FlyFish0825/lamost_broad/just外接板/picture/QQ20260525-173408.png

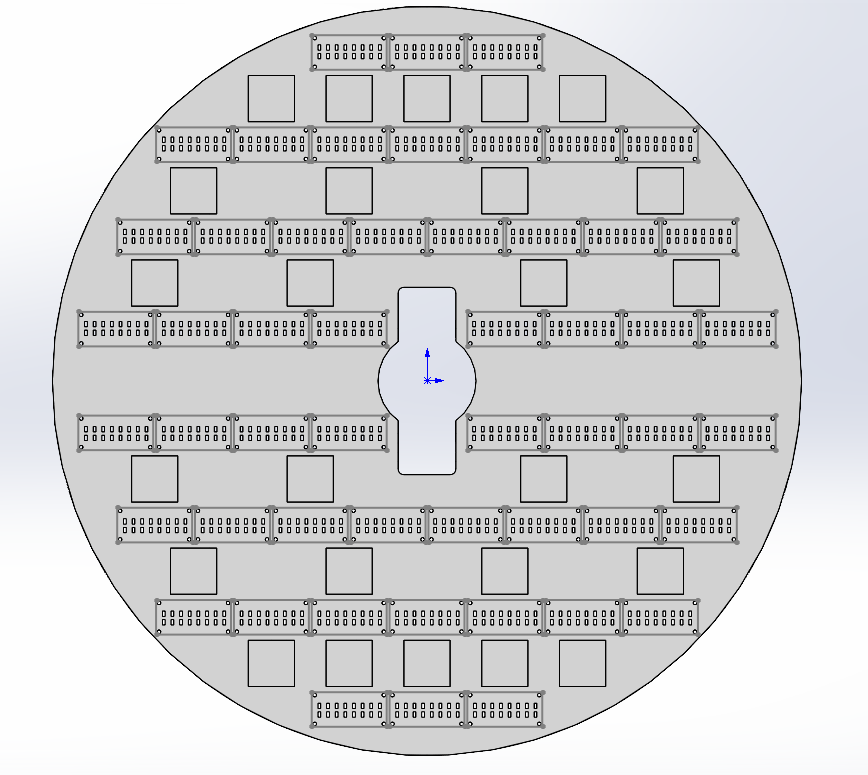
just外接板/picture/QQ20260525-173408.png
