FlyFish0825/lamost_broad/just外接板/picture/光纤示意2.png

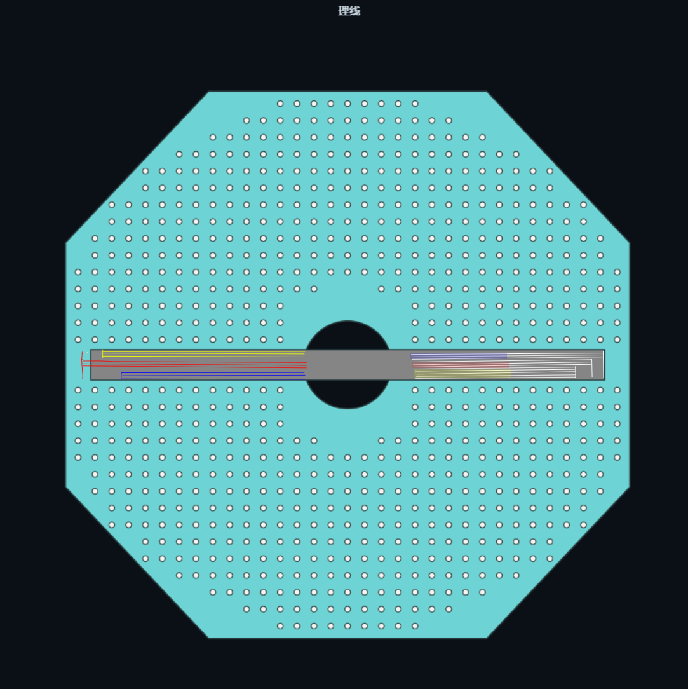
just外接板/picture/光纤示意2.png
