FlyFish0825/lamost_broad/just外接板/picture/光纤示意.png

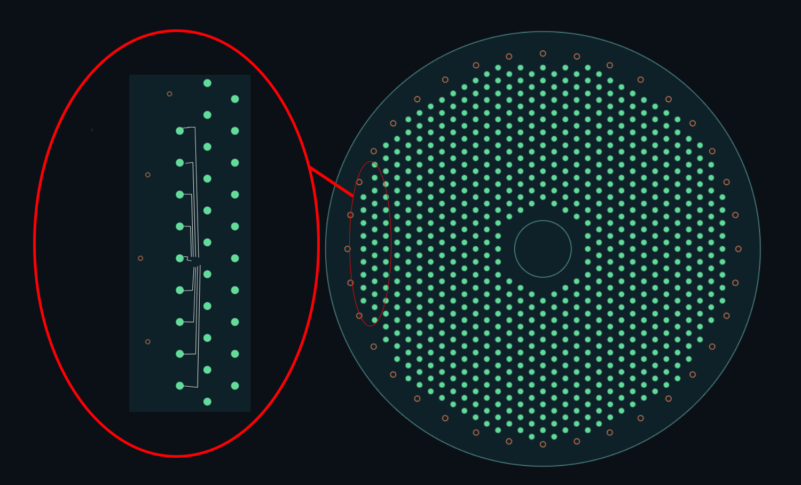
just外接板/picture/光纤示意.png
