FlyFish0825/lamost_broad/just外接板/picture/微信图片_20260402115239_76_106.jpg

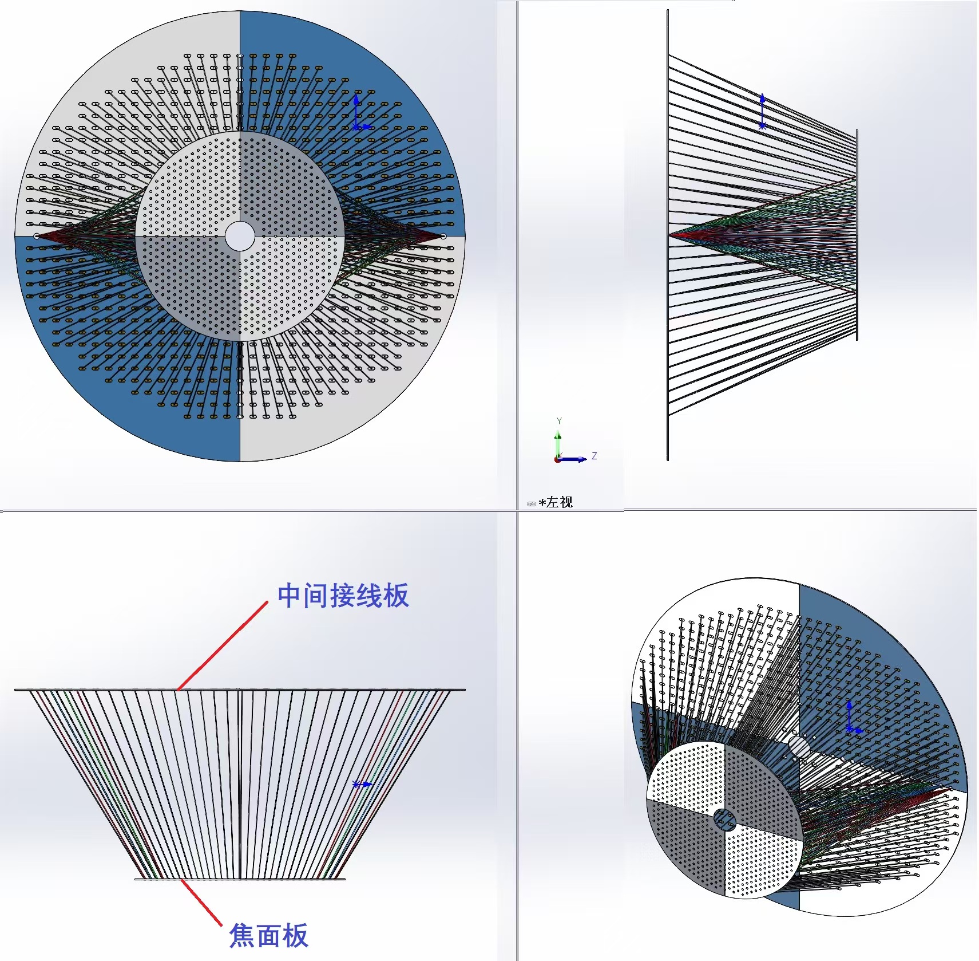
just外接板/picture/微信图片_20260402115239_76_106.jpg
