FlyFish0825/lamost_broad/just外接板/picture/微信图片_20260402115243_80_106.jpg

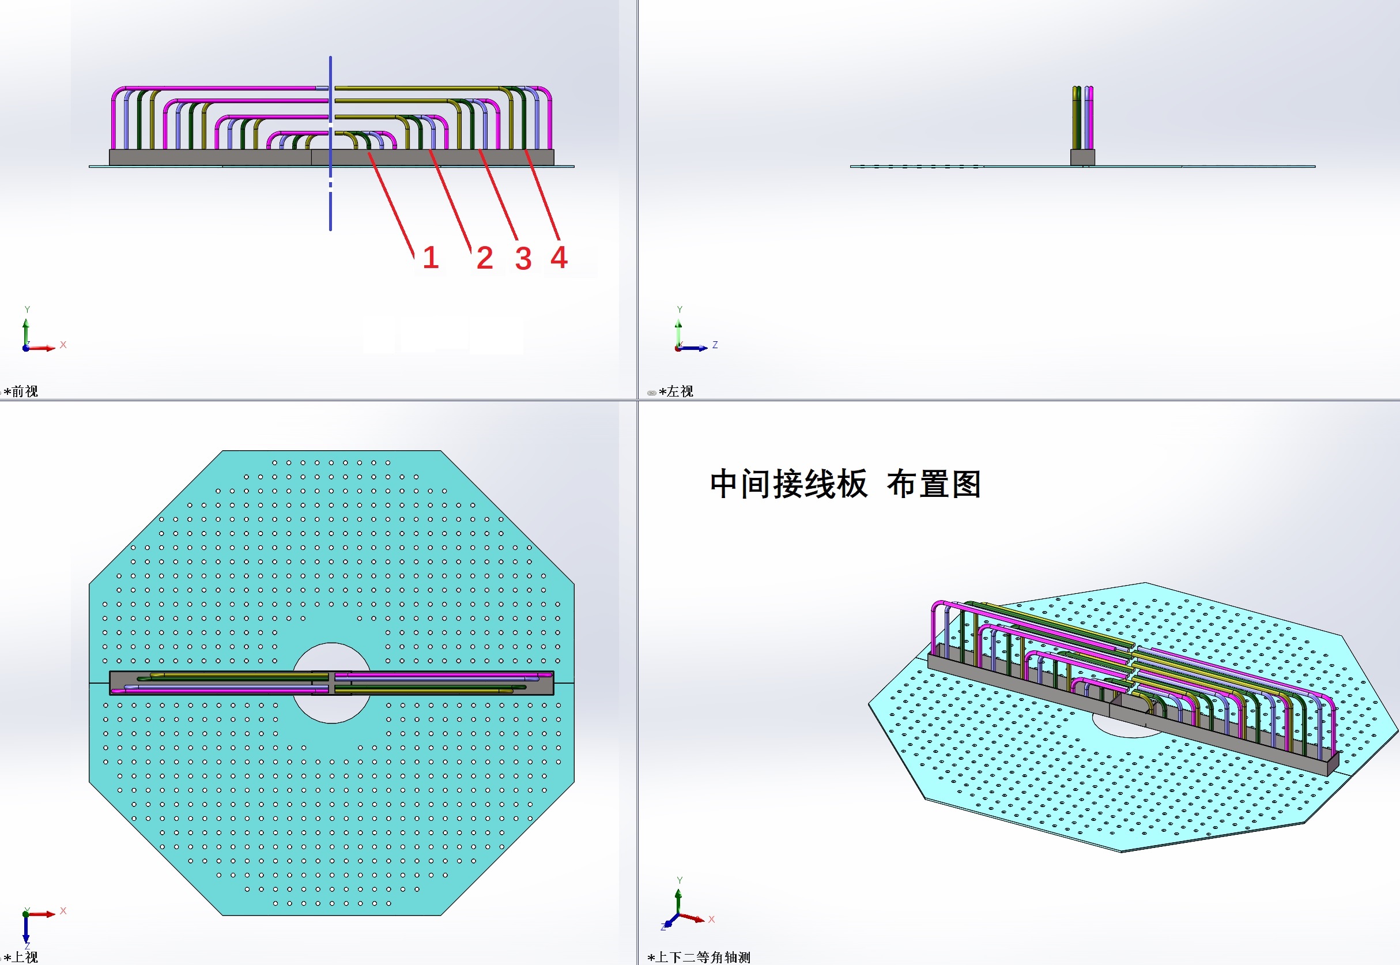
just外接板/picture/微信图片_20260402115243_80_106.jpg
