FlyFish0825/lamost_broad/just外接板/picture/数目.png

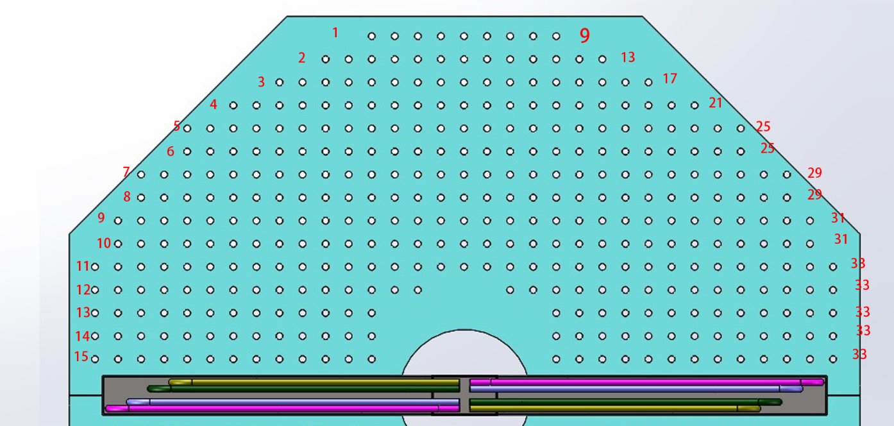
just外接板/picture/数目.png
