FlyFish0825/lamost_broad/just外接板/picture/正视图.png

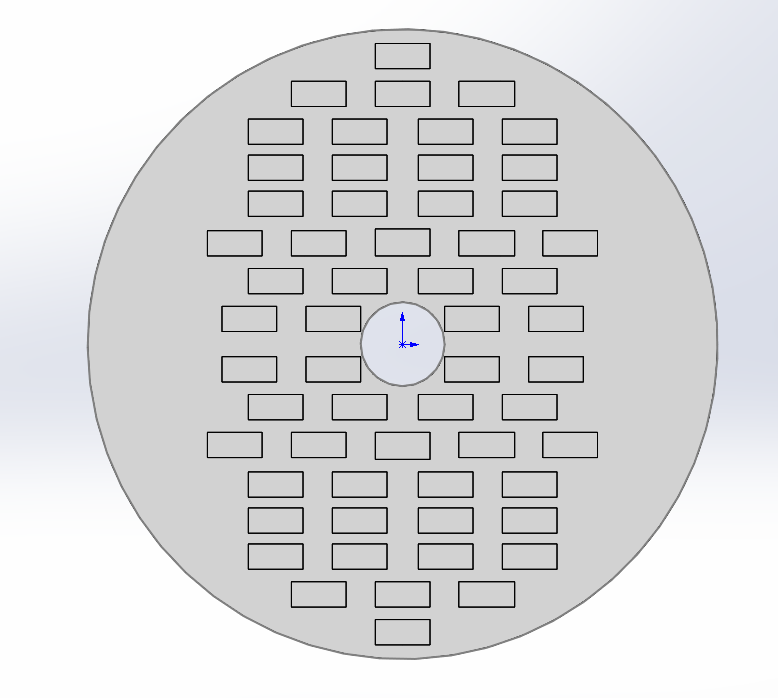
just外接板/picture/正视图.png
