FlyFish0825/lamost_broad/just外接板/picture/示意图2.jpg

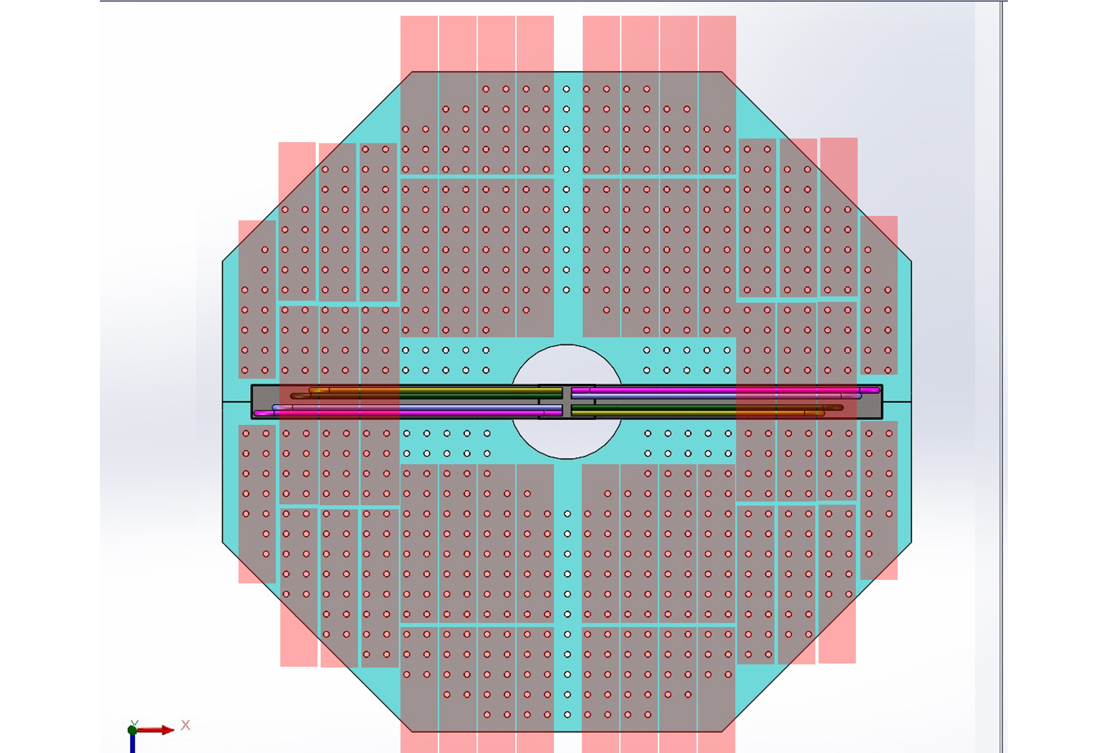
just外接板/picture/示意图2.jpg
