FlyFish0825/lamost_broad/lamost_broad_MCU/Core/pcb_broad/just_led.c

#include "just_led.h"
#include "main.h"


// 外部单元映射：数组下标 0~15 对应 USB1/LED1 ~ USB16/LED16
// 数组值 N 表示 Canvas 单元 AN，0 表示该端口未使用
#if PCB_ID == 1
const uint16_t pcb_map[JUST_BOARD_LED_NUMBER] = {
    0U, 0U, 0U, 0U, 0U, 0U, 0U, 0U,
    221U, 281U, 249U, 248U, 278U, 252U, 280U, 279U
};
#elif PCB_ID == 2
const uint16_t pcb_map[JUST_BOARD_LED_NUMBER] = {
    305U, 329U, 301U, 374U, 396U, 420U, 421U, 445U,
    304U, 328U, 351U, 373U, 352U, 419U, 397U, 444U
};
#elif PCB_ID == 3
const uint16_t pcb_map[JUST_BOARD_LED_NUMBER] = {
    0U, 0U, 0U, 0U, 0U, 0U, 0U, 0U,
    471U, 473U, 502U, 472U, 499U, 474U, 500U, 0U
};
#elif PCB_ID == 4
const uint16_t pcb_map[JUST_BOARD_LED_NUMBER] = {
    0U, 0U, 0U, 0U, 0U, 0U, 77U, 98U,
    0U, 0U, 0U, 0U, 0U, 75U, 76U, 142U
};
#elif PCB_ID == 5
const uint16_t pcb_map[JUST_BOARD_LED_NUMBER] = {
    121U, 168U, 170U, 146U, 145U, 220U, 171U, 219U,
    97U, 99U, 143U, 144U, 122U, 167U, 169U, 195U
};
#elif PCB_ID == 6
const uint16_t pcb_map[JUST_BOARD_LED_NUMBER] = {
    197U, 224U, 223U, 251U, 250U, 303U, 302U, 327U,
    196U, 222U, 194U, 247U, 276U, 275U, 277U, 300U
};
#elif PCB_ID == 7
const uint16_t pcb_map[JUST_BOARD_LED_NUMBER] = {
    326U, 349U, 350U, 372U, 371U, 395U, 394U, 418U,
    325U, 348U, 347U, 370U, 369U, 392U, 393U, 417U
};
#elif PCB_ID == 8
const uint16_t pcb_map[JUST_BOARD_LED_NUMBER] = {
    443U, 442U, 501U, 470U, 529U, 528U, 498U, 555U,
    440U, 441U, 468U, 469U, 497U, 552U, 527U, 526U
};
#elif PCB_ID == 9
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
    282U, 330U, 307U, 375U, 377U, 399U, 398U, 422U
};
#elif PCB_ID == 52
const uint16_t pcb_map[JUST_BOARD_LED_NUMBER] = {
    448U, 447U, 475U, 449U, 478U, 446U, 477U, 0U,
    0U, 0U, 0U, 0U, 0U, 0U, 0U, 0U
};
#else
#error "PCB_ID must be between 1 and 52"
#endif

// LED mapping: LED1..LED16
PCB_Broad_LED pcb_leds[16] = {
    {GPIOA, GPIO_PIN_0, 0},  // LED1 PA0
    {GPIOA, GPIO_PIN_1, 0},  // LED2 PA1
    {GPIOA, GPIO_PIN_2, 0},  // LED3 PA2
    {GPIOA, GPIO_PIN_3, 0},  // LED4 PA3
    {GPIOA, GPIO_PIN_4, 0},  // LED5 PA4
    {GPIOA, GPIO_PIN_5, 0},  // LED6 PA5
    {GPIOA, GPIO_PIN_6, 0},  // LED7 PA6
    {GPIOA, GPIO_PIN_7, 0},  // LED8 PA7
    {GPIOA, GPIO_PIN_8, 0},  // LED9 PA8
    {GPIOB, GPIO_PIN_0, 0},  // LED10 PB0
    {GPIOA, GPIO_PIN_15, 0}, // LED11 PA15
    {GPIOB, GPIO_PIN_3, 0},  // LED12 PB3
    {GPIOB, GPIO_PIN_4, 0},  // LED13 PB4
    {GPIOB, GPIO_PIN_5, 0},  // LED14 PB5
    {GPIOB, GPIO_PIN_6, 0},  // LED15 PB6
    {GPIOB, GPIO_PIN_7, 0},  // LED16 PB7
};




/**
 * @brief  点亮指定编号的 LED（常亮）
 * @param  led_id : LED 序号（0 ~ JUST_BOARD_LED_NUMBER-1）
 * @note   该函数直接操作 GPIO 输出高电平，需确保引脚已初始化为推挽输出
 */
void just_led_light(uint16_t led_id) {
  if (led_id < JUST_BOARD_LED_NUMBER) {
    PCB_Broad_LED PCB_LED = pcb_leds[led_id];
    HAL_GPIO_WritePin(PCB_LED.port, PCB_LED.pin, 1); // 点亮LED
  }
}


/**
 * @brief  熄灭指定编号的 LED
 * @param  led_id : LED 序号（0 ~ JUST_BOARD_LED_NUMBER-1）
 */
void just_led_Delight(uint16_t led_id) {
  if (led_id < JUST_BOARD_LED_NUMBER) {
    PCB_Broad_LED PCB_LED = pcb_leds[led_id];
    HAL_GPIO_WritePin(PCB_LED.port, PCB_LED.pin, 0); // 熄灭LED
  }
}



/**
 * @brief  设置指定 LED 的工作状态
 * @param  led_id : LED 序号
 * @param  state  : 状态值，0=熄灭，1=常亮，2=闪烁
 * @note   该函数仅更新软件状态标志，实际亮灭由定时器中断回调统一处理
 */
void just_led_control(uint16_t led_id, uint8_t state)
{
    if (led_id < JUST_BOARD_LED_NUMBER) {
        pcb_leds[led_id].state = state; // 更新LED状态
    }
}



/**
 * @brief  TIM1 溢出中断回调函数（实现 LED 闪烁及调光）
 * @param  htim : 指向触发中断的定时器句柄
 * @note   每发生一次溢出中断，全局计数器递增；达到阈值后翻转闪烁相位。
 *         然后遍历所有 LED，根据其 state 决定是否点亮；
 *         点亮操作会打开 LED，随后的 OC 中断负责熄灭，形成简易 PWM。
 */
void HAL_TIM_PeriodElapsedCallback(TIM_HandleTypeDef *htim) {
  static uint8_t blink_counter = 0; // 溢出中断计数器
  static uint8_t blink_phase = 1;   // 当前亮灭状态：1-亮，0-灭
  if (htim->Instance == TIM1) {
    // 在这里处理 TIM1 的周期性中断事件
    // 例如，切换 LED 状态或执行其他定时任务
    // ------ 闪烁节拍控制（每进一次溢出中断计一次） ------
        blink_counter++;
        if (blink_counter >= 50) {      // 26 → 闪烁频率约 2 Hz
            blink_counter = 0;
            blink_phase = !blink_phase;
        }

      // 遍历所有 LED，根据各自状态决定是否点亮
      for (uint8_t i = 0; i < JUST_BOARD_LED_NUMBER; i++) {
        uint8_t state = pcb_leds[i].state;
        uint8_t should_light = 0;

        if (state == 1) {
          should_light = 1; // 常亮
        } else if (state == 2) {
          should_light = blink_phase; // 闪烁，跟随全局相位
        } // state == 0 则 should_light 保持 0，不点亮

        if (should_light) {
          just_led_light(i); // 进入 PWM 点亮周期（之后由 OC 中断熄灭）
        }
      }
    }
  }



  /**
 * @brief  TIM1 输出比较中断回调（用于熄灭所有 LED，完成 PWM 周期）
 * @param  htim : 指向触发中断的定时器句柄
 * @note   在 OC 事件发生时，强制关闭所有 LED 输出，与溢出中断配合实现调光。
 */
void HAL_TIM_OC_DelayElapsedCallback(TIM_HandleTypeDef *htim) {

  if (htim->Instance == TIM1) {
    // 在这里处理 TIM1 的输出比较中断事件
    // 例如，切换 LED 状态或执行其他定时任务
    for (uint8_t i = 0; i < JUST_BOARD_LED_NUMBER; i++) {
      just_led_Delight(i);
    }
  }
}
