FlyFish0825/lamost_broad/lamost_broad_MCU/Core/Src/can.c

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
/* Includes ------------------------------------------------------------------*/
#include "can.h"

CAN_HandleTypeDef hcan;

/* CAN init function */
void MX_CAN_Init(void)
{

  hcan.Instance = CAN;
  hcan.Init.Prescaler = 8;
  hcan.Init.Mode = CAN_MODE_NORMAL;
  hcan.Init.SyncJumpWidth = CAN_SJW_1TQ;
  hcan.Init.TimeSeg1 = CAN_BS1_12TQ;
  hcan.Init.TimeSeg2 = CAN_BS2_5TQ;
  hcan.Init.TimeTriggeredMode = DISABLE;
  hcan.Init.AutoBusOff = DISABLE;
  hcan.Init.AutoWakeUp = DISABLE;
  hcan.Init.AutoRetransmission = DISABLE;
  hcan.Init.ReceiveFifoLocked = DISABLE;
  hcan.Init.TransmitFifoPriority = DISABLE;
  if (HAL_CAN_Init(&hcan) != HAL_OK)
  {
    Error_Handler();
  }
  /* USER CODE BEGIN CAN_Init 2 */
  CAN_FilterTypeDef sFilterConfig;
  sFilterConfig.FilterBank = 0;
  sFilterConfig.FilterMode = CAN_FILTERMODE_IDMASK;
  sFilterConfig.FilterScale = CAN_FILTERSCALE_32BIT;
  sFilterConfig.FilterIdHigh = 0x0000;
  sFilterConfig.FilterIdLow = 0x0000;
  sFilterConfig.FilterMaskIdHigh = 0x0000;
  sFilterConfig.FilterMaskIdLow = 0x0000;
  sFilterConfig.FilterFIFOAssignment = CAN_RX_FIFO0;
  sFilterConfig.FilterActivation = ENABLE;
  sFilterConfig.SlaveStartFilterBank = 14;
  if (HAL_CAN_ConfigFilter(&hcan, &sFilterConfig) != HAL_OK)
  {
      Error_Handler();
  }
  /* USER CODE END CAN_Init 2 */

}

void HAL_CAN_MspInit(CAN_HandleTypeDef* canHandle)
{

  GPIO_InitTypeDef GPIO_InitStruct = {0};
  if(canHandle->Instance==CAN)
  {
    /* CAN clock enable */
    __HAL_RCC_CAN1_CLK_ENABLE();

    __HAL_RCC_GPIOA_CLK_ENABLE();
    /**CAN GPIO Configuration
    PA11     ------> CAN_RX
    PA12     ------> CAN_TX
    */
    GPIO_InitStruct.Pin = GPIO_PIN_11|GPIO_PIN_12;
    GPIO_InitStruct.Mode = GPIO_MODE_AF_PP;
    GPIO_InitStruct.Pull = GPIO_NOPULL;
    GPIO_InitStruct.Speed = GPIO_SPEED_FREQ_HIGH;
    GPIO_InitStruct.Alternate = GPIO_AF9_CAN;
    HAL_GPIO_Init(GPIOA, &GPIO_InitStruct);

    /* CAN interrupt Init */
    HAL_NVIC_SetPriority(USB_LP_CAN_RX0_IRQn, 0, 0);
    HAL_NVIC_EnableIRQ(USB_LP_CAN_RX0_IRQn);
    HAL_NVIC_SetPriority(CAN_RX1_IRQn, 0, 0);
    HAL_NVIC_EnableIRQ(CAN_RX1_IRQn);
  }
}

void HAL_CAN_MspDeInit(CAN_HandleTypeDef* canHandle)
{

  if(canHandle->Instance==CAN)
  {
    /* Peripheral clock disable */
    __HAL_RCC_CAN1_CLK_DISABLE();

    /**CAN GPIO Configuration
    PA11     ------> CAN_RX
    PA12     ------> CAN_TX
    */
    HAL_GPIO_DeInit(GPIOA, GPIO_PIN_11|GPIO_PIN_12);

    /* CAN interrupt Deinit */
    HAL_NVIC_DisableIRQ(USB_LP_CAN_RX0_IRQn);
    HAL_NVIC_DisableIRQ(CAN_RX1_IRQn);
  }
}
